coalShork/MZ-ISA/mz100ISA.kicad_sch

## KiCad design mz100ISA.kicad_sch (2026-01-08)

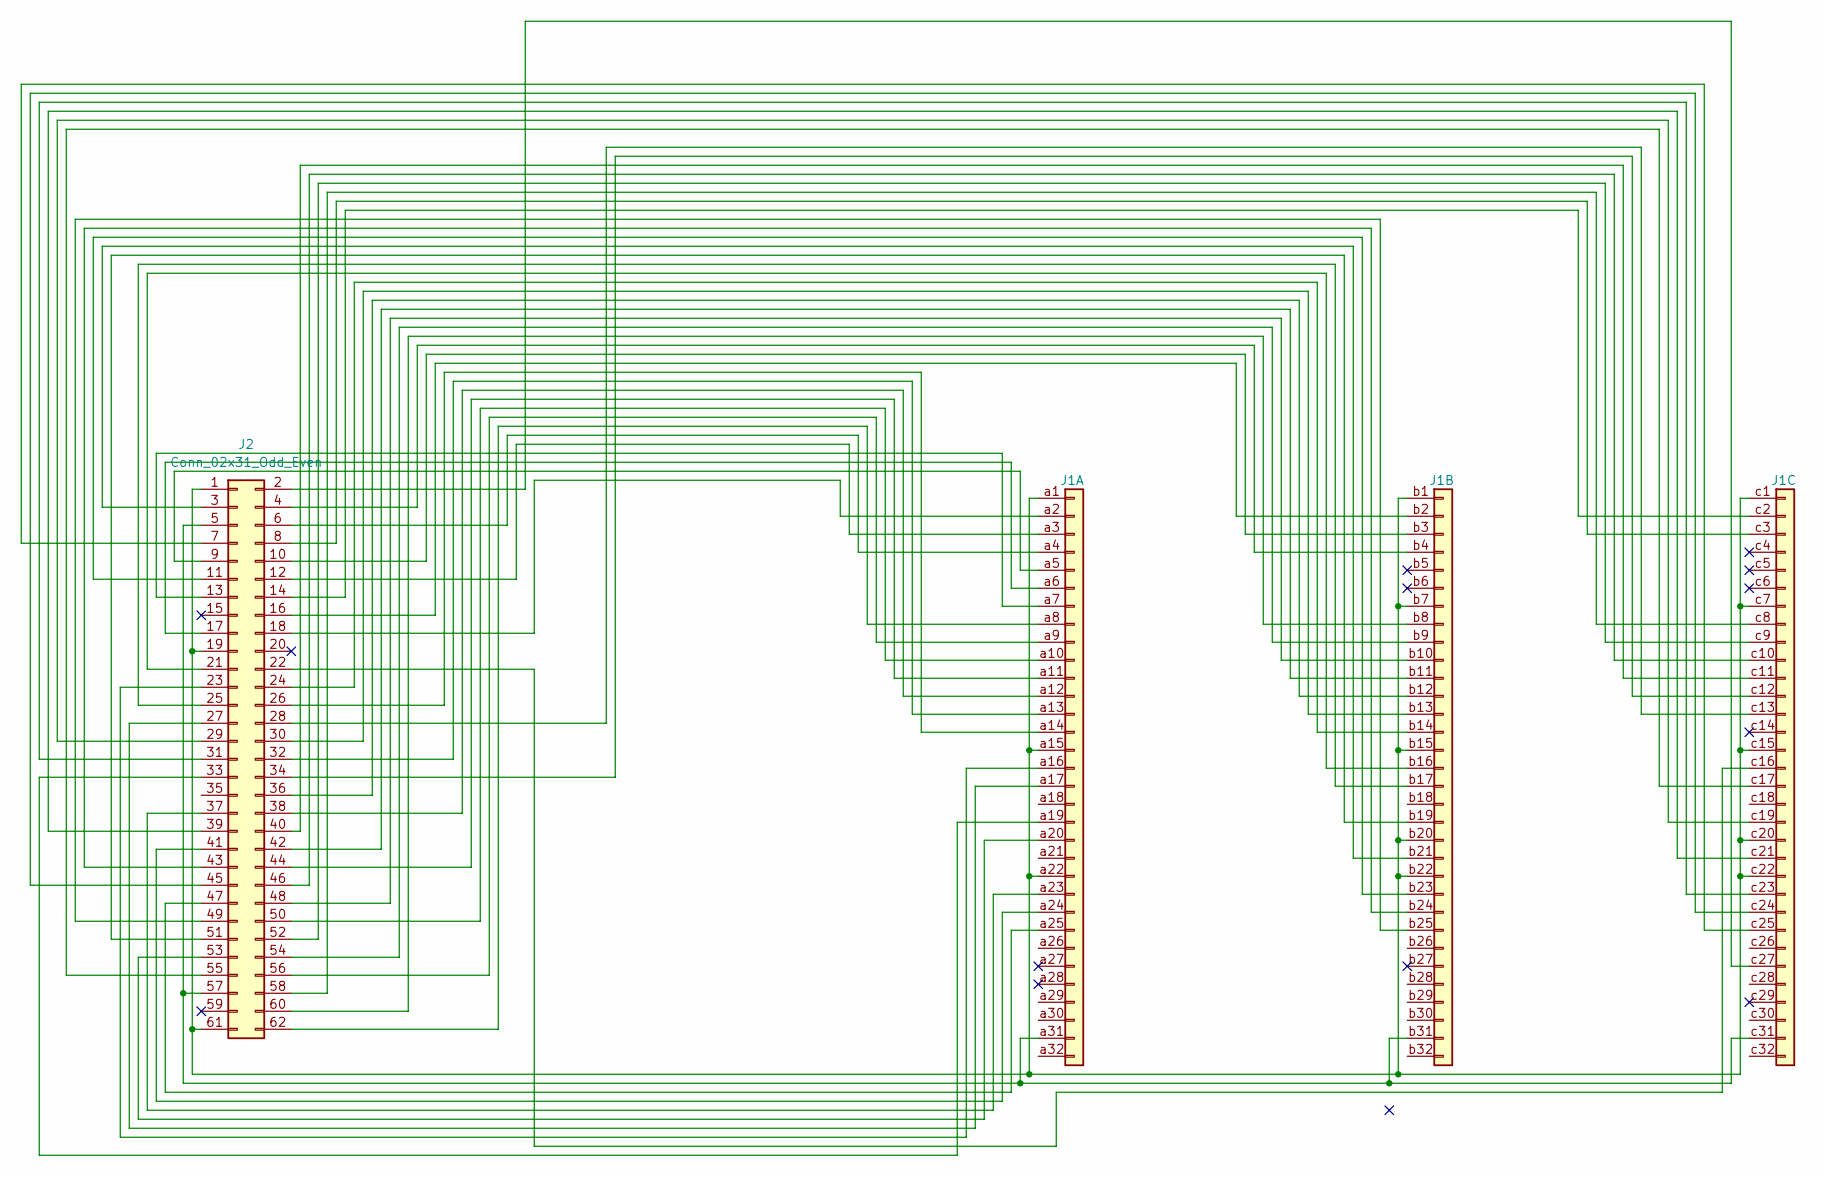
[picture p5: schematic mz100ISA.kicad_sch]

Parts:
J1: MZ Exp Bus; DIN41612_C_3x32_Male_Horizontal_THT
J2: Conn_02x31_Odd_Even; ISA_8BIT_SOCKET

Connections:
unnamed: J1.a1, J1.a15, J1.a22, J1.b1, J1.b7, J1.b15, J1.b20, J1.b22, J1.c1, J1.c7, J1.c15, J1.c20, J1.c22, J2.1, J2.19, J2.61
unnamed: J1.a2, J2.18
unnamed: J1.a3, J2.12
unnamed: J1.a4, J2.6
unnamed: J1.a5, J2.9
unnamed: J1.a6, J2.17
unnamed: J1.a7, J2.13
unnamed: J1.a8, J2.62
unnamed: J1.a9, J2.56
unnamed: J1.a10, J2.50
unnamed: J1.a11, J2.44
unnamed: J1.a12, J2.38
unnamed: J1.a13, J2.32
unnamed: J1.a14, J2.26
unnamed: J1.a16, J2.23
unnamed: J1.a17, J2.27
unnamed: J1.a19, J2.33
unnamed: J1.a20, J2.53
unnamed: J1.a23, J2.37
unnamed: J1.a24, J2.41
unnamed: J1.a25, J2.47
unnamed: J1.a31, J1.b31, J1.c31, J2.5, J2.57
unnamed: J1.b2, J2.16
unnamed: J1.b3, J2.10
unnamed: J1.b4, J2.4
unnamed: J1.b8, J2.60
unnamed: J1.b9, J2.54
unnamed: J1.b10, J2.48
unnamed: J1.b11, J2.42
unnamed: J1.b12, J2.36
unnamed: J1.b13, J2.30
unnamed: J1.b14, J2.24
unnamed: J1.b16, J2.21
unnamed: J1.b17, J2.25
unnamed: J1.b19, J2.51
unnamed: J1.b21, J2.3
unnamed: J1.b23, J2.11
unnamed: J1.b24, J2.43
unnamed: J1.b25, J2.49
unnamed: J1.c2, J2.14
unnamed: J1.c3, J2.8
unnamed: J1.c8, J2.58
unnamed: J1.c9, J2.52
unnamed: J1.c10, J2.46
unnamed: J1.c11, J2.40
unnamed: J1.c12, J2.34
unnamed: J1.c13, J2.28
unnamed: J1.c16, J2.22
unnamed: J1.c17, J2.55
unnamed: J1.c19, J2.29
unnamed: J1.c21, J2.39
unnamed: J1.c23, J2.31
unnamed: J1.c24, J2.45
unnamed: J1.c25, J2.7
unnamed: J1.c27, J2.2
